dimo333/Electromagic_Wand_ESP32/Software/models/1030_5/readme.txt

用的是y轴和z轴（y轴向右）

0_UpAndDown_
1_RightAngle_
2_Letter_W_
3_SharpAngle_
4_Horn_
