dimo333/Electromagic_Wand_ESP32/Hardware/PCB/PCB_v1.0/readme.md

关于PCB_v1.0:
===
这是我画的第一块能使用的魔杖板，它集成了红外、蓝牙以及WIFI.<br>
但它并不是完美的。<br>
我最初绘制它时过于压缩板子的长宽，以至于它的顶端只保留有1x6p的外接端口<br>
这极大的影响了我后续为它设计的外接模块。<br>
但它也并非一无是处，它的功能一切正常.<br>
