dimo333/Electromagic_Wand_ESP32/Hardware/PCB/PCB_v2.0/readme.md

关于PCB_v2.0:
===
在这一版当中，我将顶端改成了2x3p的外接排针<br>
同时我考虑到并不是所有人都需要红外，所以我移除了板子上原来集成的红外发射的功能，并将其单独做成了个外接模块。<br>
