dimo333/Electromagic_Wand_ESP32/Software/models/0922_6/0922_6_gestures.jpg

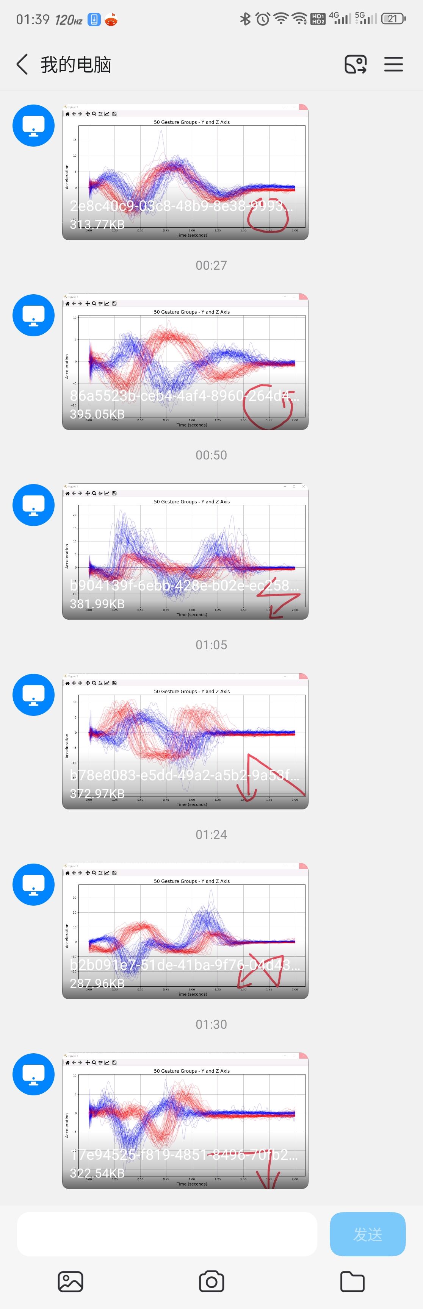
Software/models/0922_6/0922_6_gestures.jpg
