dimo333/Electromagic_Wand_ESP32/Software/models/1030_5/5.png

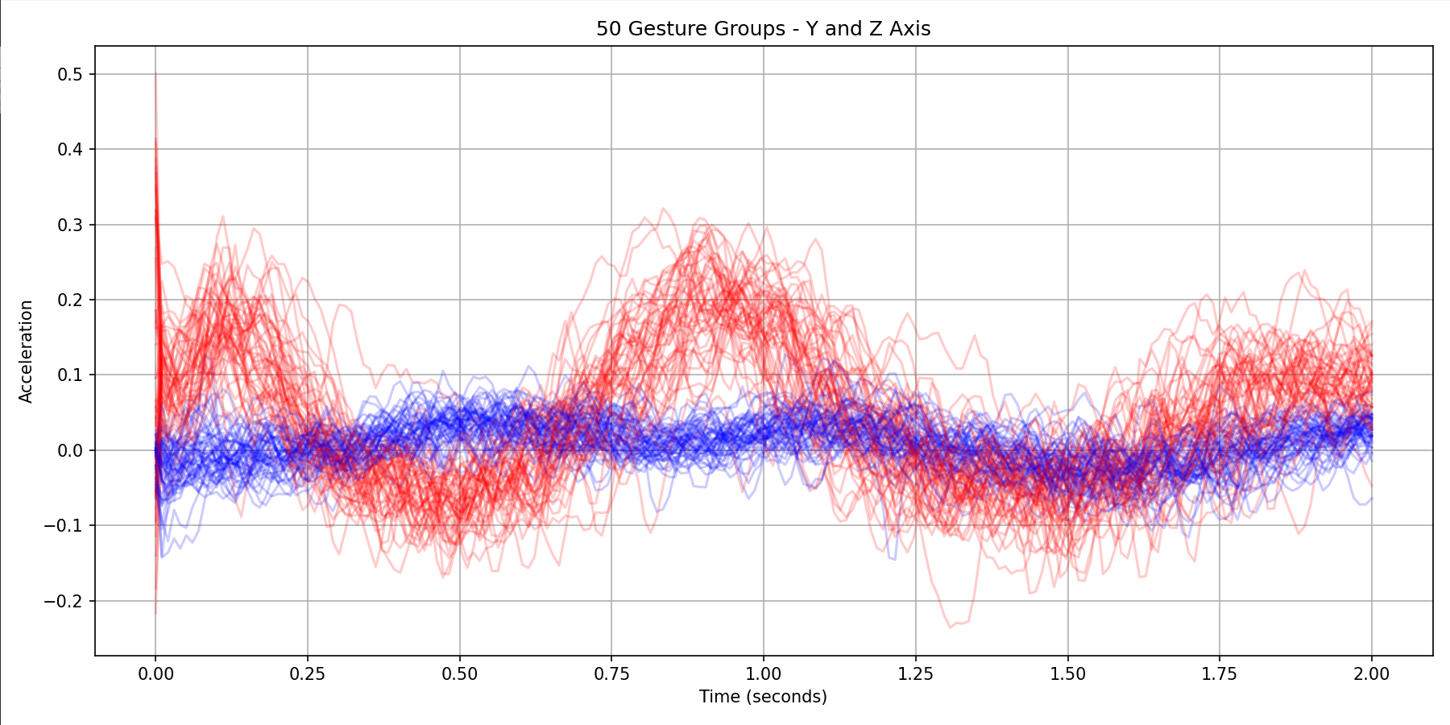
Software/models/1030_5/5.png
