dimo333/Electromagic_Wand_ESP32/Software/Others/wand_experiments-/ESP_BLE_Mouse/ESP32_wroom_xz/readme.md

关于ESP_BLE_Mouse:
===
实际运行起来还不错，可以试试，这一个目前是使用了x轴和z轴，适用于大块的esp32-wroom

最后的最后：
===
不要忘了看注释
