dimo333/Electromagic_Wand_ESP32/Software/Others/wand_variants-/wand_3_variants/model.h

unsigned char model_tflite[] = {
  0x1c, 0x00, 0x00, 0x00, 0x54, 0x46, 0x4c, 0x33, 0x14, 0x00, 0x20, 0x00,
  0x04, 0x00, 0x08, 0x00, 0x0c, 0x00, 0x10, 0x00, 0x14, 0x00, 0x00, 0x00,
  0x18, 0x00, 0x1c, 0x00, 0x14, 0x00, 0x00, 0x00, 0x03, 0x00, 0x00, 0x00,
  0x18, 0x00, 0x00, 0x00, 0x30, 0x00, 0x00, 0x00, 0xe4, 0x00, 0x00, 0x00,
  0x30, 0x00, 0x00, 0x00, 0x8c, 0x00, 0x00, 0x00, 0x84, 0x00, 0x00, 0x00,
  0x06, 0x00, 0x00, 0x00, 0x04, 0x07, 0x00, 0x00, 0x5c, 0x06, 0x00, 0x00,
  0x58, 0x05, 0x00, 0x00, 0xb0, 0x03, 0x00, 0x00, 0xfc, 0x02, 0x00, 0x00,
  0xbc, 0x01, 0x00, 0x00, 0x01, 0x00, 0x00, 0x00, 0xd8, 0x00, 0x00, 0x00,
  0x16, 0x00, 0x00, 0x00, 0xac, 0x66, 0x00, 0x00, 0xa8, 0x66, 0x00, 0x00,
  0xe8, 0x65, 0x00, 0x00, 0x48, 0x65, 0x00, 0x00, 0xa4, 0x64, 0x00, 0x00,
  0x04, 0x64, 0x00, 0x00, 0x88, 0x63, 0x00, 0x00, 0x34, 0x63, 0x00, 0x00,
  0xd8, 0x62, 0x00, 0x00, 0x8c, 0x5a, 0x00, 0x00, 0xbc, 0x58, 0x00, 0x00,
  0x68, 0x0d, 0x00, 0x00, 0x10, 0x07, 0x00, 0x00, 0x78, 0x66, 0x00, 0x00,
  0x74, 0x66, 0x00, 0x00, 0x70, 0x66, 0x00, 0x00, 0x6c, 0x66, 0x00, 0x00,
  0x68, 0x66, 0x00, 0x00, 0x64, 0x66, 0x00, 0x00, 0x60, 0x66, 0x00, 0x00,
  0x5c, 0x66, 0x00, 0x00, 0x3c, 0x00, 0x00, 0x00, 0x00, 0x00, 0x00, 0x00,
  0x01, 0x00, 0x00, 0x00, 0x0c, 0x00, 0x00, 0x00, 0x08, 0x00, 0x0c, 0x00,
  0x04, 0x00, 0x08, 0x00, 0x08, 0x00, 0x00, 0x00, 0x08, 0x00, 0x00, 0x00,
  0x15, 0x00, 0x00, 0x00, 0x13, 0x00, 0x00, 0x00, 0x6d, 0x69, 0x6e, 0x5f,
  0x72, 0x75, 0x6e, 0x74, 0x69, 0x6d, 0x65, 0x5f, 0x76, 0x65, 0x72, 0x73,
  0x69, 0x6f, 0x6e, 0x00, 0xa6, 0x9a, 0xff, 0xff, 0x04, 0x00, 0x00, 0x00,
  0x10, 0x00, 0x00, 0x00, 0x31, 0x2e, 0x31, 0x30, 0x2e, 0x30, 0x00, 0x00,
  0x00, 0x00, 0x00, 0x00, 0x00, 0x00, 0x00, 0x00, 0x0f, 0x00, 0x00, 0x00,
  0x4d, 0x4c, 0x49, 0x52, 0x20, 0x43, 0x6f, 0x6e, 0x76, 0x65, 0x72, 0x74,
  0x65, 0x64, 0x2e, 0x00, 0x00, 0x00, 0x0e, 0x00, 0x18, 0x00, 0x04, 0x00,
  0x08, 0x00, 0x0c, 0x00, 0x10, 0x00, 0x14, 0x00, 0x0e, 0x00, 0x00, 0x00,
  0x14, 0x00, 0x00, 0x00, 0x64, 0x00, 0x00, 0x00, 0x68, 0x00, 0x00, 0x00,
  0x6c, 0x00, 0x00, 0x00, 0x8c, 0x00, 0x00, 0x00, 0x14, 0x00, 0x00, 0x00,
  0x74, 0x65, 0x00, 0x00, 0x20, 0x65, 0x00, 0x00, 0x9c, 0x64, 0x00, 0x00,
  0x08, 0x64, 0x00, 0x00, 0x68, 0x63, 0x00, 0x00, 0xc4, 0x62, 0x00, 0x00,
  0x60, 0x62, 0x00, 0x00, 0x08, 0x62, 0x00, 0x00, 0xb0, 0x61, 0x00, 0x00,
  0x60, 0x59, 0x00, 0x00, 0x8c, 0x57, 0x00, 0x00, 0x34, 0x0c, 0x00, 0x00,
  0xd4, 0x05, 0x00, 0x00, 0x2c, 0x05, 0x00, 0x00, 0x28, 0x04, 0x00, 0x00,
  0x10, 0x03, 0x00, 0x00, 0x7c, 0x02, 0x00, 0x00, 0xc8, 0x01, 0x00, 0x00,
  0x00, 0x01, 0x00, 0x00, 0x84, 0x00, 0x00, 0x00, 0x01, 0x00, 0x00, 0x00,
  0x00, 0x00, 0x00, 0x00, 0x01, 0x00, 0x00, 0x00, 0x13, 0x00, 0x00, 0x00,
  0x08, 0x00, 0x00, 0x00, 0x64, 0x05, 0x00, 0x00, 0xb8, 0x04, 0x00, 0x00,
  0x98, 0x03, 0x00, 0x00, 0x9c, 0x02, 0x00, 0x00, 0x14, 0x02, 0x00, 0x00,
  0x44, 0x01, 0x00, 0x00, 0x98, 0x00, 0x00, 0x00, 0x10, 0x00, 0x00, 0x00,
  0x04, 0x00, 0x00, 0x00, 0x6d, 0x61, 0x69, 0x6e, 0x00, 0x00, 0x00, 0x00,
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
};
unsigned int model_tflite_len = 26388;
