dimo333/Electromagic_Wand_ESP32/Software/Others/wand_experiments-/ESP_BLE_KeyBoard/ESP_BLE_KeyBoard/ESP_BLE_KeyBoard.ino

#include <BleKeyboard.h>

BleKeyboard bleKeyboard;

void setup() {
  Serial.begin(115200);
  Serial.println("Starting BLE work!");
  bleKeyboard.begin();
}

void loop() {
  if(bleKeyboard.isConnected()) {
    Serial.println("Sending 'Hello world'...");
    bleKeyboard.print("Hello world");

    delay(500);
//
//    Serial.println("Sending Enter key...");
//    bleKeyboard.write(KEY_RETURN);
//
//    delay(1000);
//


   //
   // Below is an example of pressing multiple keyboard modifiers 
   // which by default is commented out.
    /*
    Serial.println("Sending Ctrl+Alt+Delete...");
    bleKeyboard.press(KEY_LEFT_CTRL);
    bleKeyboard.press(KEY_LEFT_ALT);
    bleKeyboard.press(KEY_DELETE);
    delay(100);
    bleKeyboard.releaseAll();
    */
  }

  Serial.println("Waiting 5 seconds...");
  delay(5000);
}
